13dcreator/13DCreator-Filament-Maker/ESP8266_13dcfilamentmaker/ESP8266 Heater Control V1.jpg

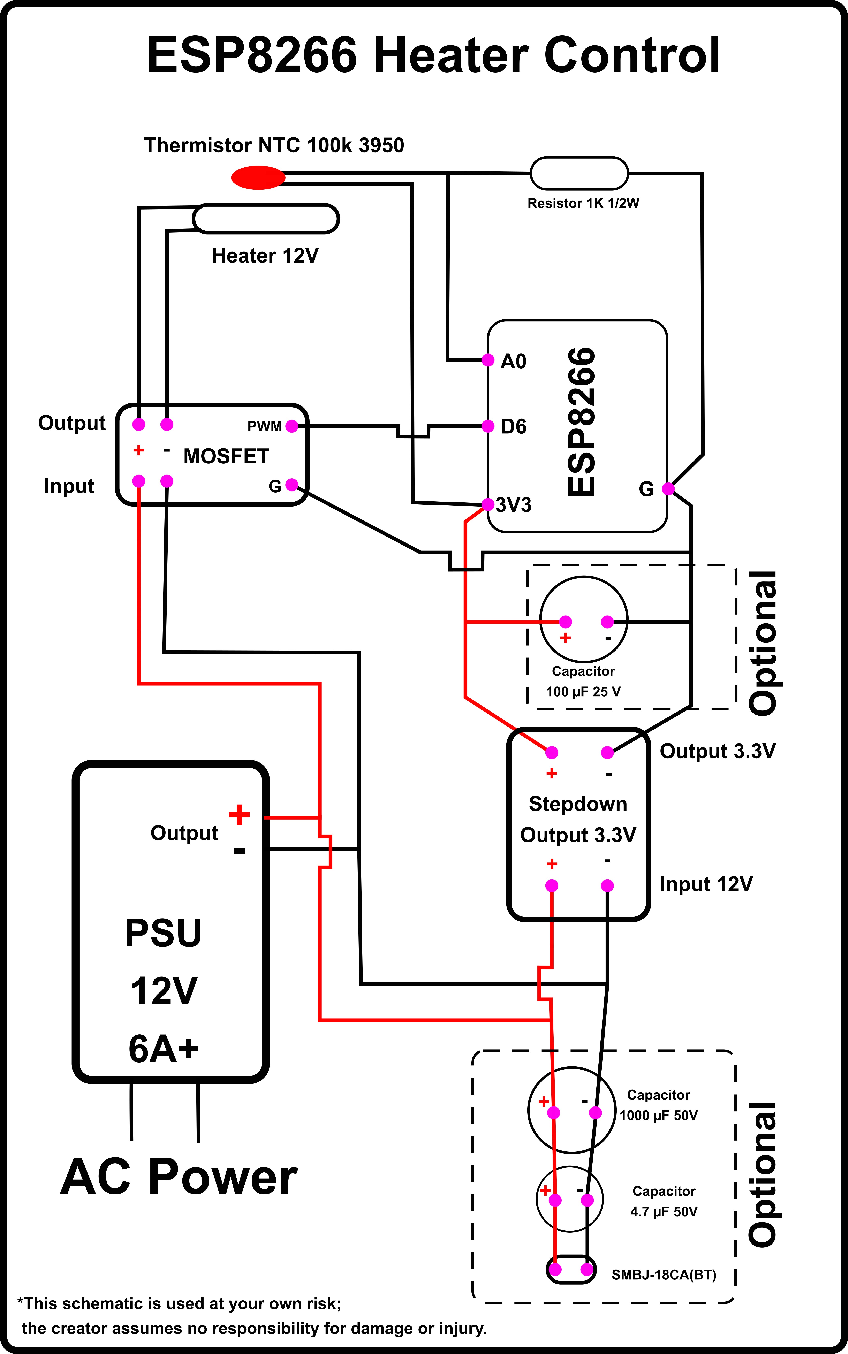
ESP8266_13dcfilamentmaker/ESP8266 Heater Control V1.jpg
