13dcreator/13DCreator-Filament-Maker/Stl/Cutter/Guide Bottle Cutter Spacer.stl

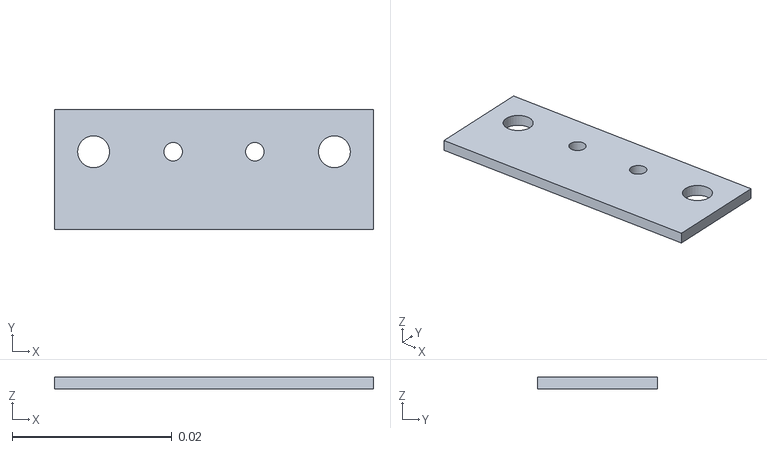
[picture p42: CAD file, 2024-11-10]
Stl/Cutter/Guide Bottle Cutter Spacer.stl
0.04 x 0.015 x 0.0015
