13dcreator/13DCreator-Filament-Maker/Stl/Dynamo WIK25GAD027/WIK25GAD027 Gear.stl

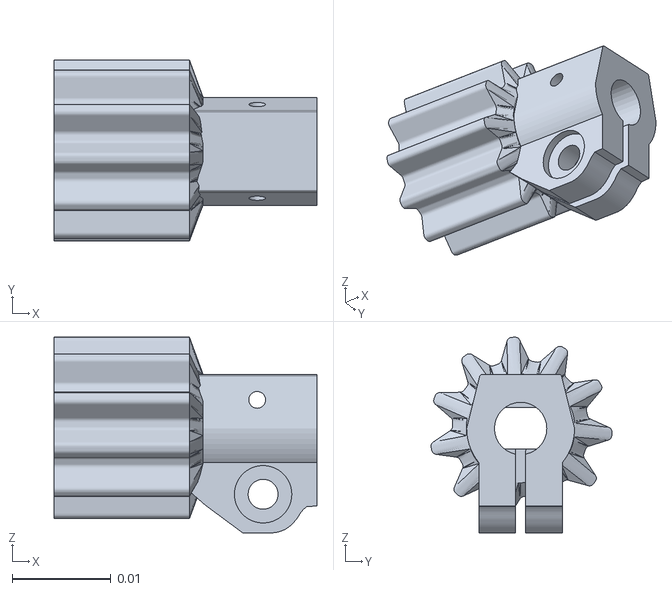
[picture p43: CAD file, 2025-12-24]
Stl/Dynamo WIK25GAD027/WIK25GAD027 Gear.stl
0.0266 x 0.0183 x 0.0198
