13dcreator/13DCreator-Filament-Maker/Stl/Filament Puller/Filament Puller Lock1 V2.stl

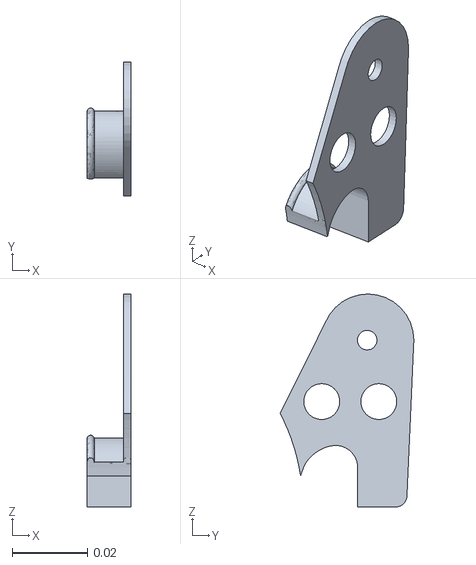
[picture p44: CAD file, 2025-02-04]
Stl/Filament Puller/Filament Puller Lock1 V2.stl
0.0117 x 0.0356 x 0.0566
