13dcreator/13DCreator-Filament-Maker/Stl/Filament Straightener/Filament Straightener V2.stl

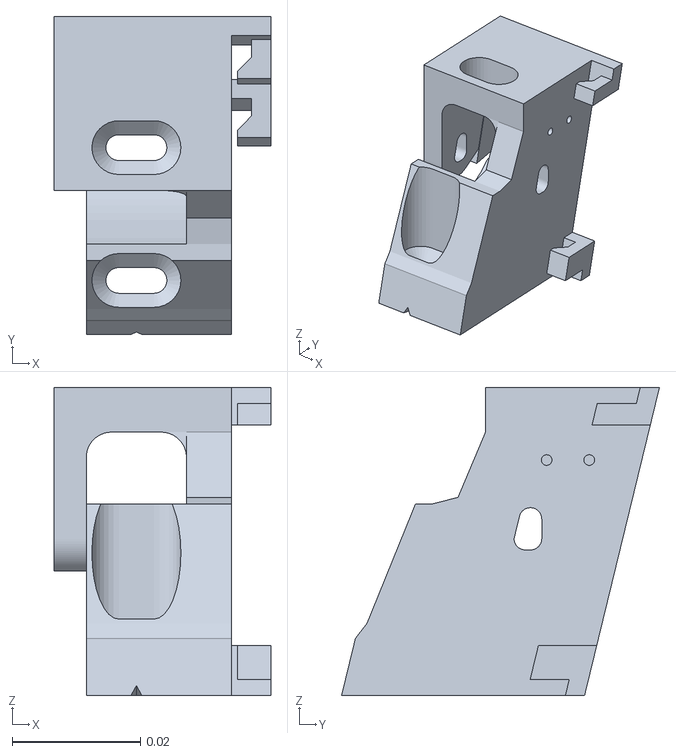
[picture p45: CAD file, 2025-02-04]
Stl/Filament Straightener/Filament Straightener V2.stl
0.0338 x 0.0496 x 0.0481
