13dcreator/13DCreator-Filament-Maker/Stl/Panel/Panel Rear Dimmer.stl

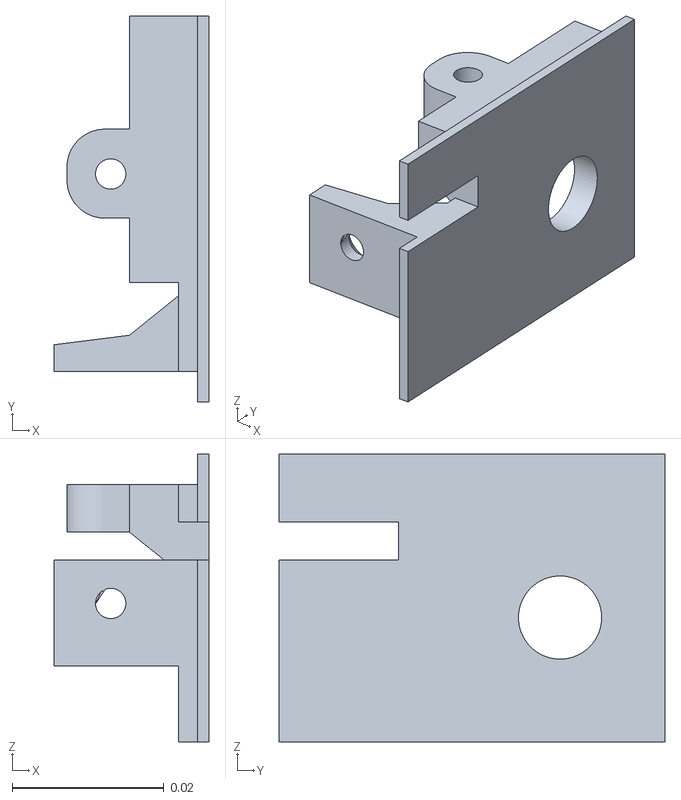
[picture p46: CAD file, 2025-12-24]
Stl/Panel/Panel Rear Dimmer.stl
0.0204 x 0.0509 x 0.038
