13dcreator/13DCreator-Filament-Maker/Stl/Stepper Motor Component/Housing N17 V2.stl

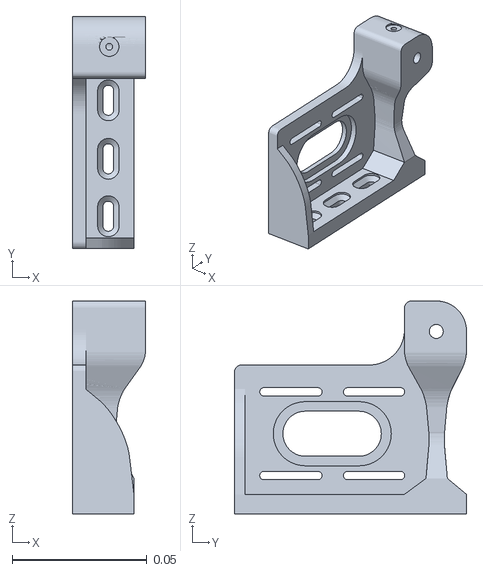
[picture p47: CAD file, 2025-02-04]
Stl/Stepper Motor Component/Housing N17 V2.stl
0.0271 x 0.086 x 0.0789
