13dcreator/13DCreator-Filament-Maker/Stl/Top Counterweight/Top Shaft Hole.stl

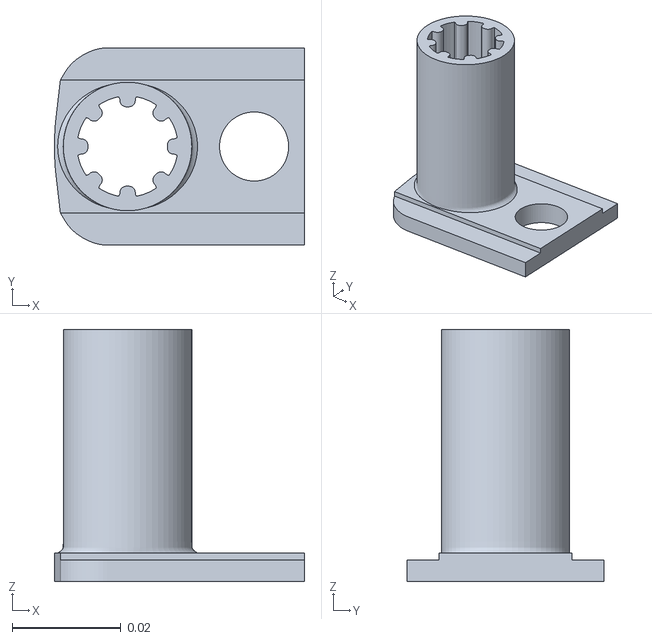
[picture p48: CAD file, 2024-10-30]
Stl/Top Counterweight/Top Shaft Hole.stl
0.0459 x 0.0363 x 0.0464
