13dcreator/13DCreator-Filament-Maker/Stl/Bottom Counterweight/Handle1 Suport.stl

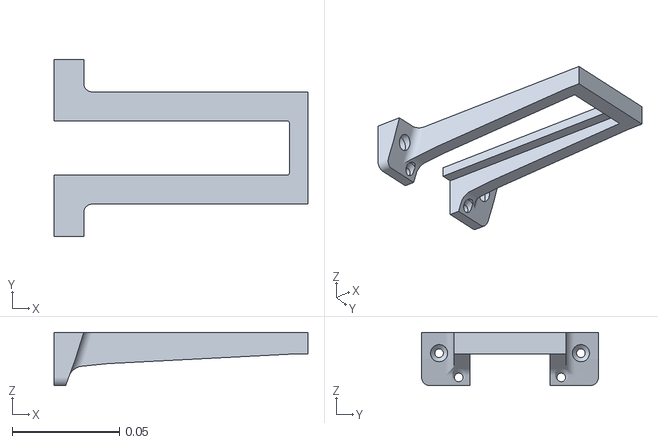
[picture p49: CAD file, 2024-11-10]
Stl/Bottom Counterweight/Handle1 Suport.stl
0.118 x 0.0825 x 0.0249
