13dcreator/13DCreator-Filament-Maker/Stl/Dynamo WIK25GAD027/Housing WIK25GAD027.stl

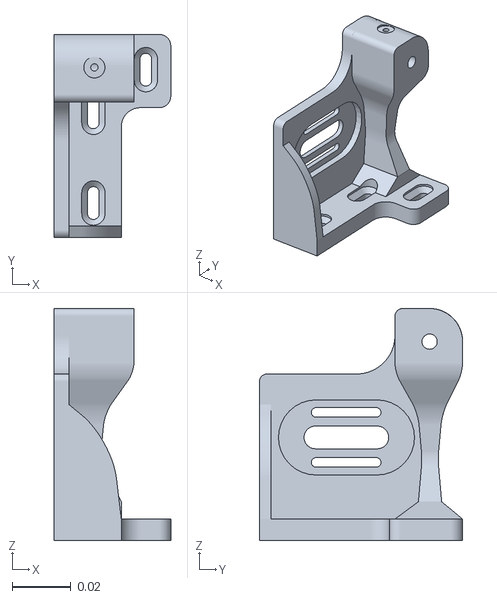
[picture p50: CAD file, 2025-12-24]
Stl/Dynamo WIK25GAD027/Housing WIK25GAD027.stl
0.0397 x 0.0691 x 0.0789
