13dcreator/13DCreator-Filament-Maker/Stl/Filament Straightener/Filament Straight Bearing.stl

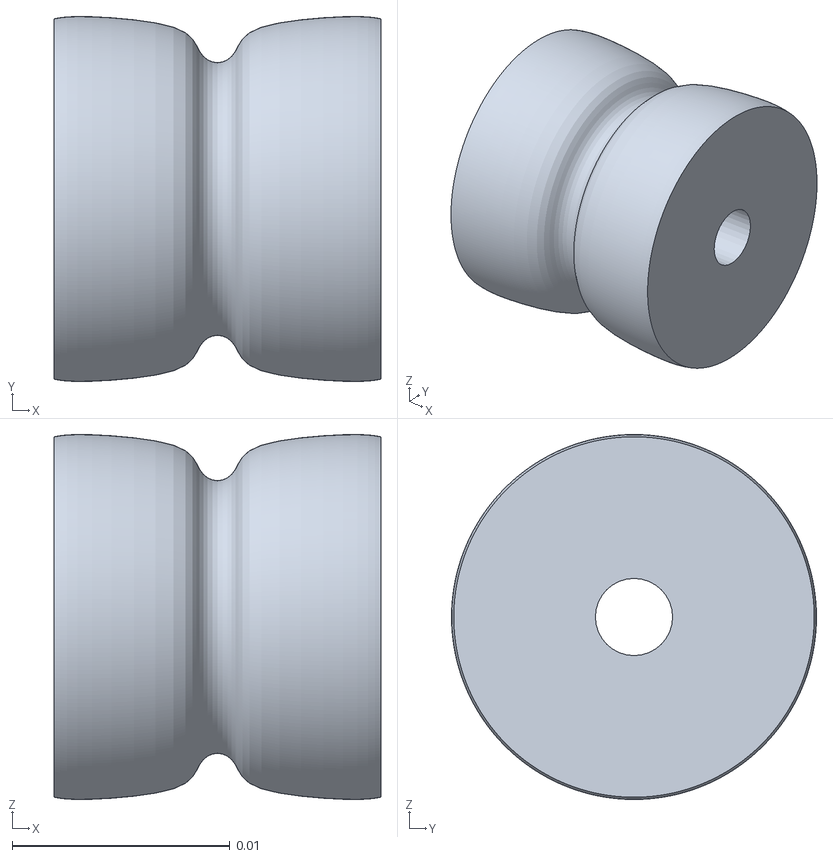
[picture p51: CAD file, 2024-10-30]
Stl/Filament Straightener/Filament Straight Bearing.stl
0.015 x 0.0167 x 0.0167
