13dcreator/13DCreator-Filament-Maker/Stl/Panel/Panel OLED V2 Bracket.stl

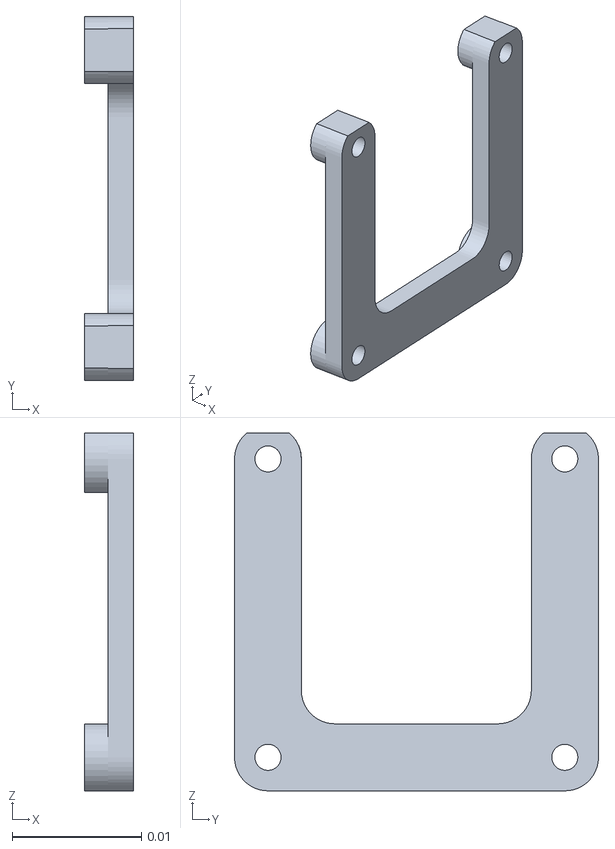
[picture p52: CAD file, 2025-12-24]
Stl/Panel/Panel OLED V2 Bracket.stl
0.00381 x 0.0282 x 0.0277
