13dcreator/13DCreator-Filament-Maker/Stl/Cutter/Spacer.stl

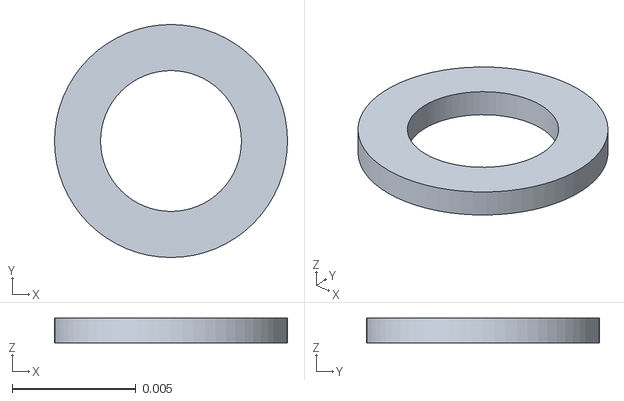
[picture p54: CAD file, 2024-10-30]
Stl/Cutter/Spacer.stl
0.0094 x 0.0094 x 0.001
