13dcreator/13DCreator-Filament-Maker/Stl/Dynamo WIK25GAD027/Primary Gear2.stl

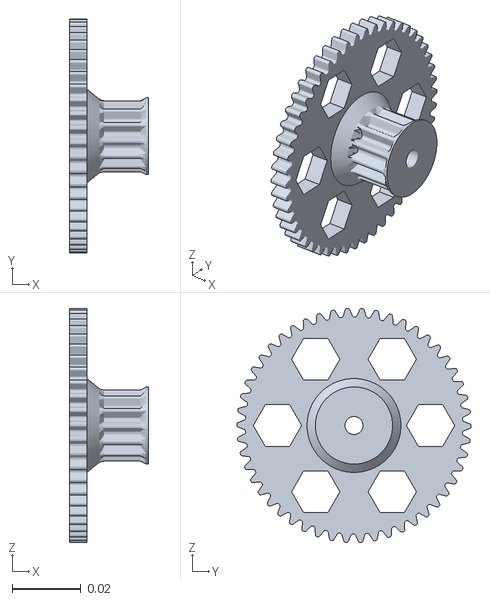
[picture p55: CAD file, 2024-10-30]
Stl/Dynamo WIK25GAD027/Primary Gear2.stl
0.0229 x 0.0682 x 0.0681
