13dcreator/13DCreator-Filament-Maker/Stl/Filament Straightener/Filament Straight.stl

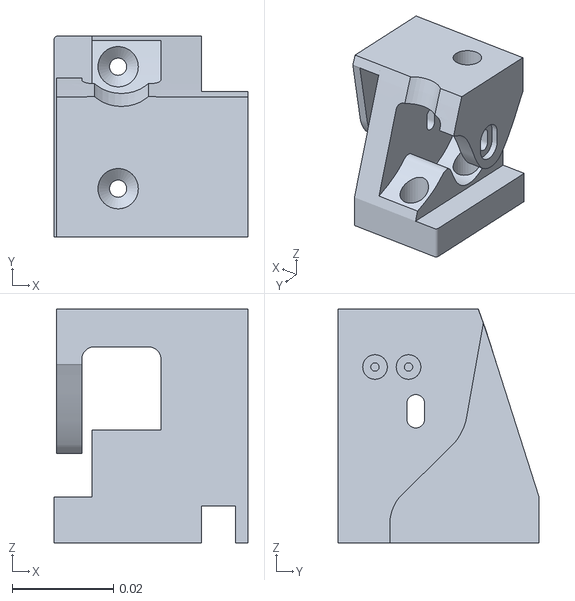
[picture p56: CAD file, 2024-10-30]
Stl/Filament Straightener/Filament Straight.stl
0.0383 x 0.0398 x 0.0463
