13dcreator/13DCreator-Filament-Maker/Stl/Stepper Motor Component/Primary Gear4 V2.stl

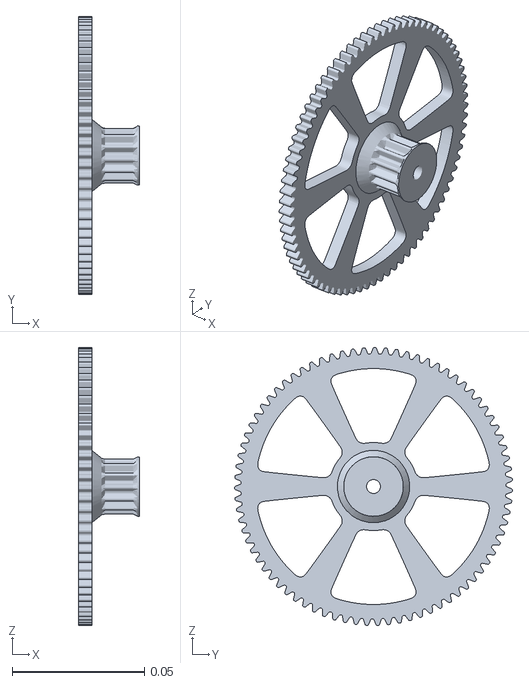
[picture p57: CAD file, 2025-02-04]
Stl/Stepper Motor Component/Primary Gear4 V2.stl
0.0229 x 0.105 x 0.105
