13dcreator/13DCreator-Filament-Maker/Stl/Panel/Panel Front Dimmer.stl

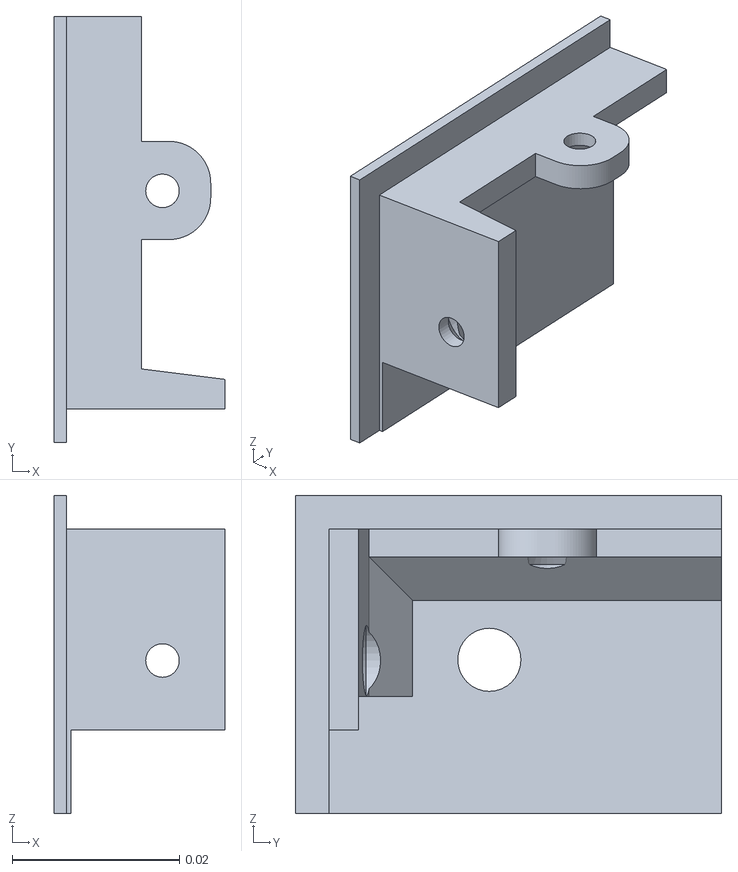
[picture p58: CAD file, 2025-12-24]
Stl/Panel/Panel Front Dimmer.stl
0.0204 x 0.0509 x 0.038
