13dcreator/13DCreator-Filament-Maker/Stl/Stepper Motor Component/Stepper Gear N23 V2.stl

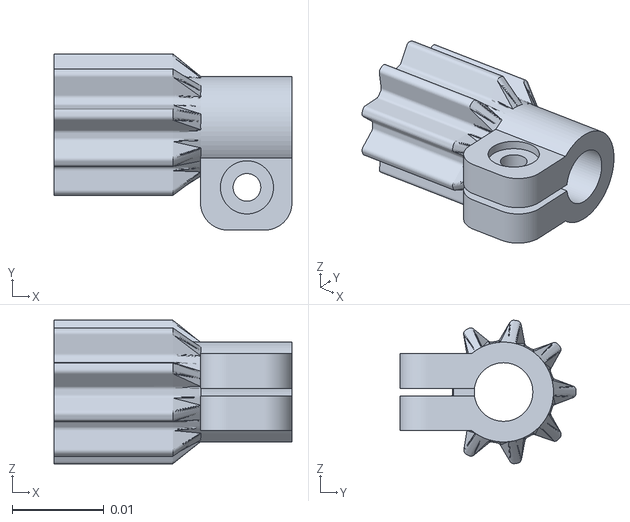
[picture p59: CAD file, 2025-02-04]
Stl/Stepper Motor Component/Stepper Gear N23 V2.stl
0.026 x 0.0193 x 0.0157
