13dcreator/13DCreator-Filament-Maker/Stl/Filament Puller/Secondary Gear.stl

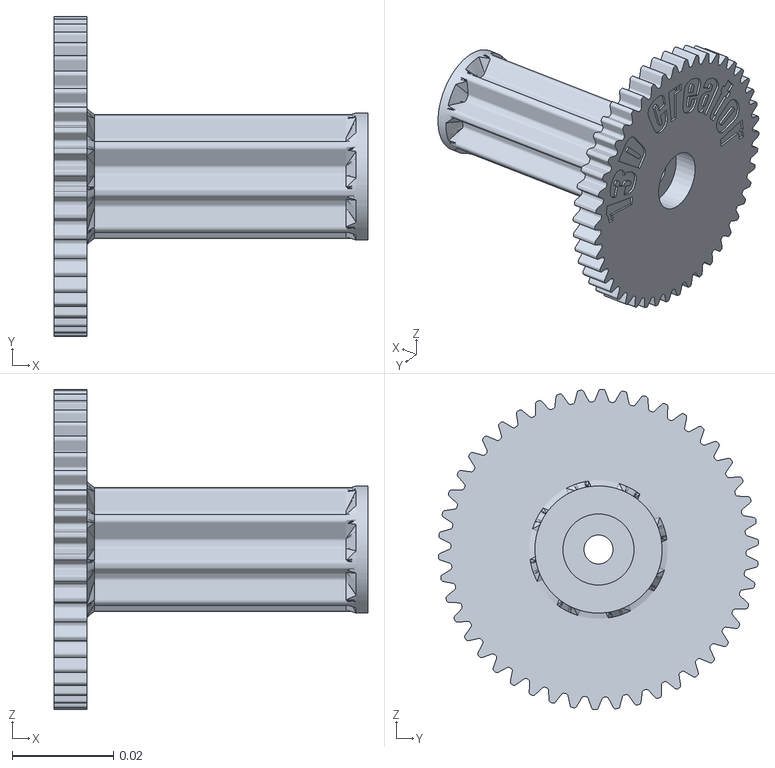
[picture p60: CAD file, 2024-10-30]
Stl/Filament Puller/Secondary Gear.stl
0.0621 x 0.0633 x 0.0634
