13dcreator/13DCreator-Filament-Maker/Stl/Stepper Motor Component/Primary Gear3.stl

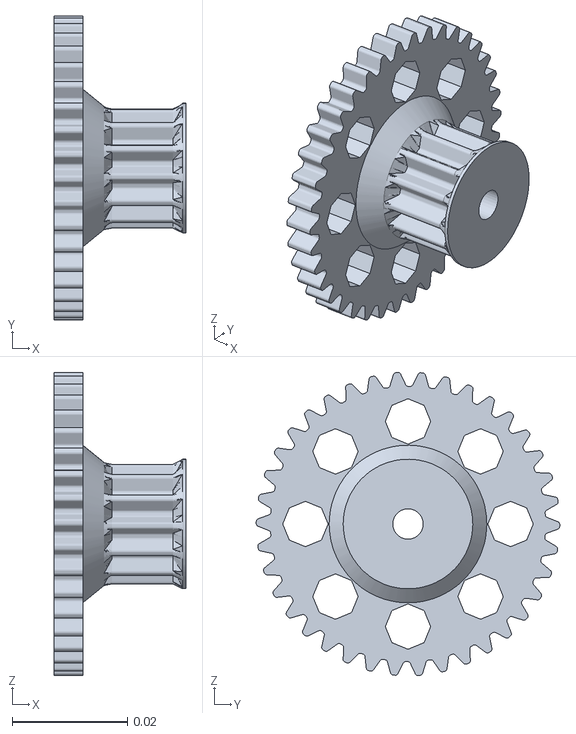
[picture p61: CAD file, 2024-10-30]
Stl/Stepper Motor Component/Primary Gear3.stl
0.0229 x 0.0527 x 0.0526
