13dcreator/13DCreator-Filament-Maker/Stl/Panel/Panel Front End (adjust to the length of the beam).stl

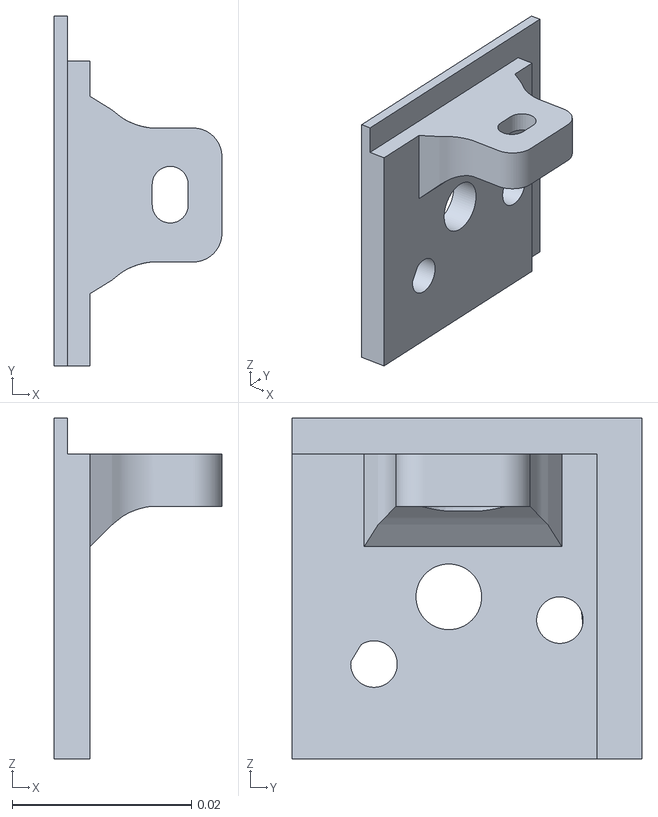
[picture p62: CAD file, 2025-12-24]
Stl/Panel/Panel Front End (adjust to the length of the beam).stl
0.0187 x 0.039 x 0.038
