13dcreator/13DCreator-Filament-Maker/Stl/Stepper Motor Component/Lock As 5mm.stl

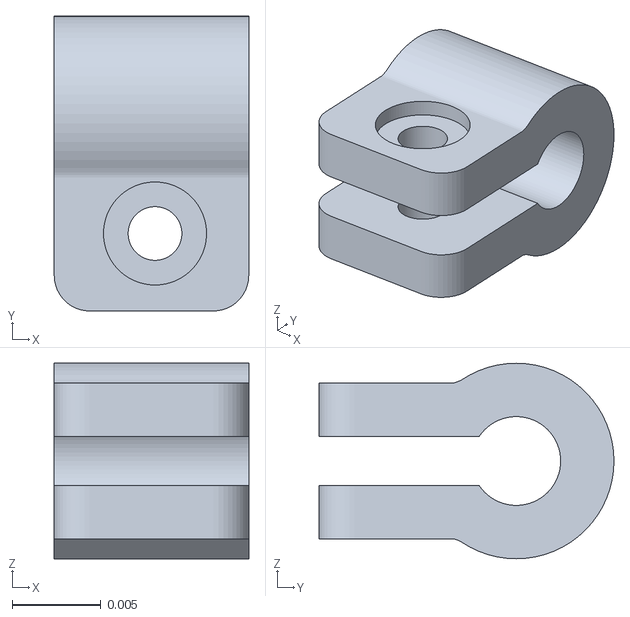
[picture p63: CAD file, 2024-10-30]
Stl/Stepper Motor Component/Lock As 5mm.stl
0.011 x 0.0166 x 0.011
