13dcreator/13DCreator-Filament-Maker/Stl/Panel/Panel Rear End (adjust to the length of the beam).stl

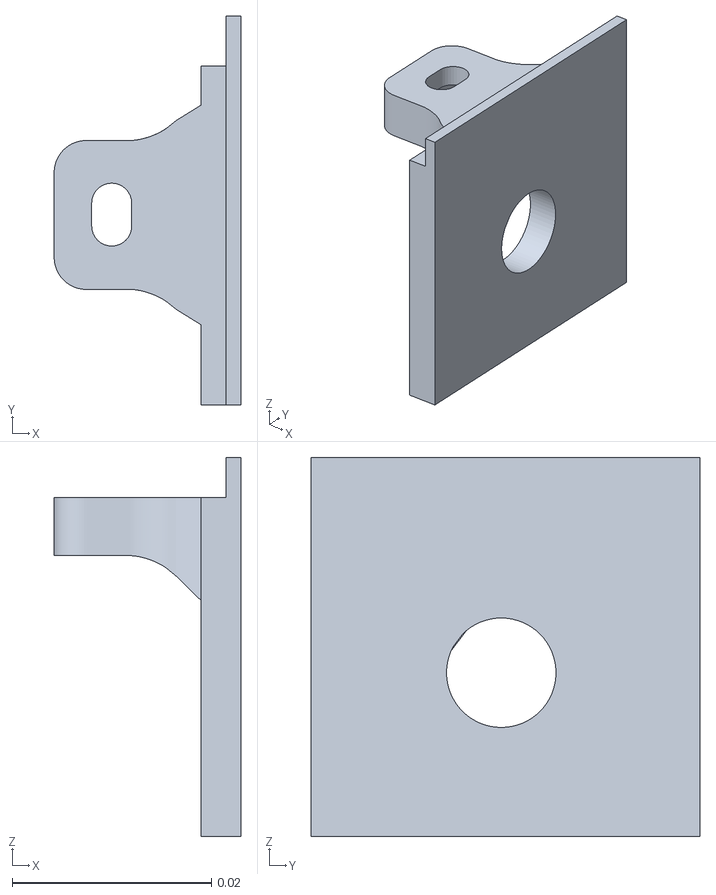
[picture p64: CAD file, 2025-12-24]
Stl/Panel/Panel Rear End (adjust to the length of the beam).stl
0.0187 x 0.039 x 0.038
