13dcreator/13DCreator-Filament-Maker/Stl/Stepper Motor Component/Primary Gear1.stl

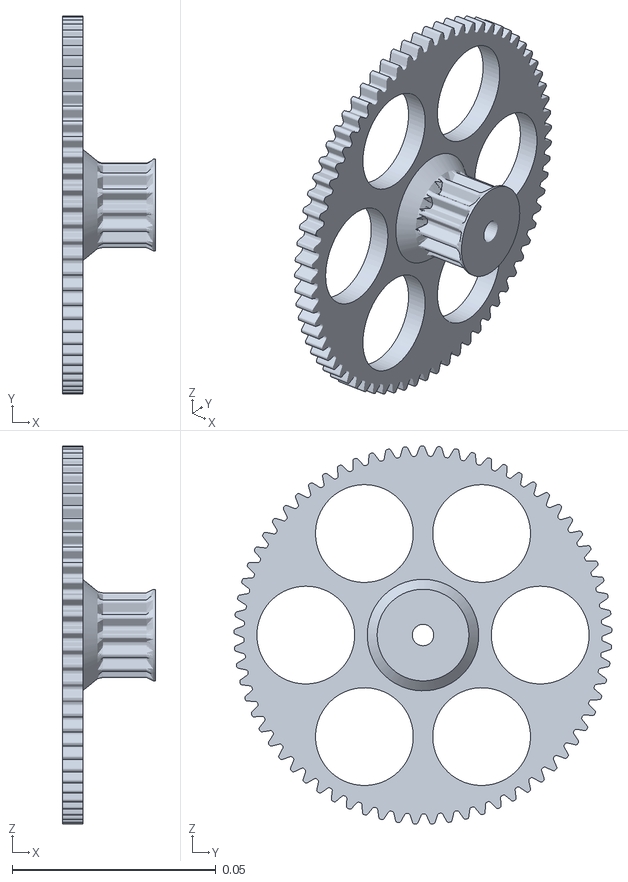
[picture p65: CAD file, 2024-10-30]
Stl/Stepper Motor Component/Primary Gear1.stl
0.0229 x 0.0927 x 0.0927
